mit41301/Intel-8085-Altaids-Computer/80C85_Computer/Software/IABENCH.BAS

100 REM   INTERFACE AGE'S BENCHMARK PROGRAM TO
110 REM   'DISCOVER' THE FIRST 1000 PRIME NUMBERS
120 REM   MODIFIED FOR PATB  5/21/17  D. HUNTER
130 PRINT "STARTING:"
140 FOR N = 1 TO 1000
150  FOR K = 2 TO 500
160   LET L = N/K
170   LET M = K*L
180   IF L = 0 GOTO 230
190   IF L = 1 GOTO 220
200   IF N > M GOTO 220
210   IF N = M GOTO 240
220  NEXT K
230  PRINT N,
240 NEXT N
250 PRINT $7
260 PRINT "FINISHED"
270 STOP
