mit41301/Intel-8085-Altaids-Computer/80C85_Computer/Software/ROLLEM.BAS

1 REM DIE ROLL
5 PRINT "LET 'EM ROLL"
10 IF INP(96) > 128 D=RND(6):GOTO 10
20 FOR I = 1 TO 30
30 D=RND(6):GOSUB 100
40 NEXT I
50 PRINT "ROLL=",D:GOTO 10
99 REM DISPLAY DIE VALUE
100 IF D=1 OUT 97,1:GOTO 180
110 IF D=2 OUT 97,2:GOTO 180
120 IF D=3 OUT 97,3:GOTO 180
130 IF D=4 OUT 97,6:GOTO 180
140 IF D=5 OUT 97,7:GOTO 180
150 IF D=6 OUT 97,14
180 RETURN
200 END
